hwaqas21343/CAGE_Radar/board1_final_3radar/secrets.example.h

// Copy this file to  secrets.h  and fill in your own values.
// secrets.h is gitignored so your credentials stay off GitHub.
#pragma once

const char* WIFI_SSID = "YOUR_WIFI_NAME";
const char* WIFI_PASS = "YOUR_WIFI_PASSWORD";
const char* LAPTOP_IP = "192.168.1.100";   // PC running the Python scope
const uint16_t UDP_PORT = 5005;
